openenergymonitor/emonpi2/docs/img/serial_config.png

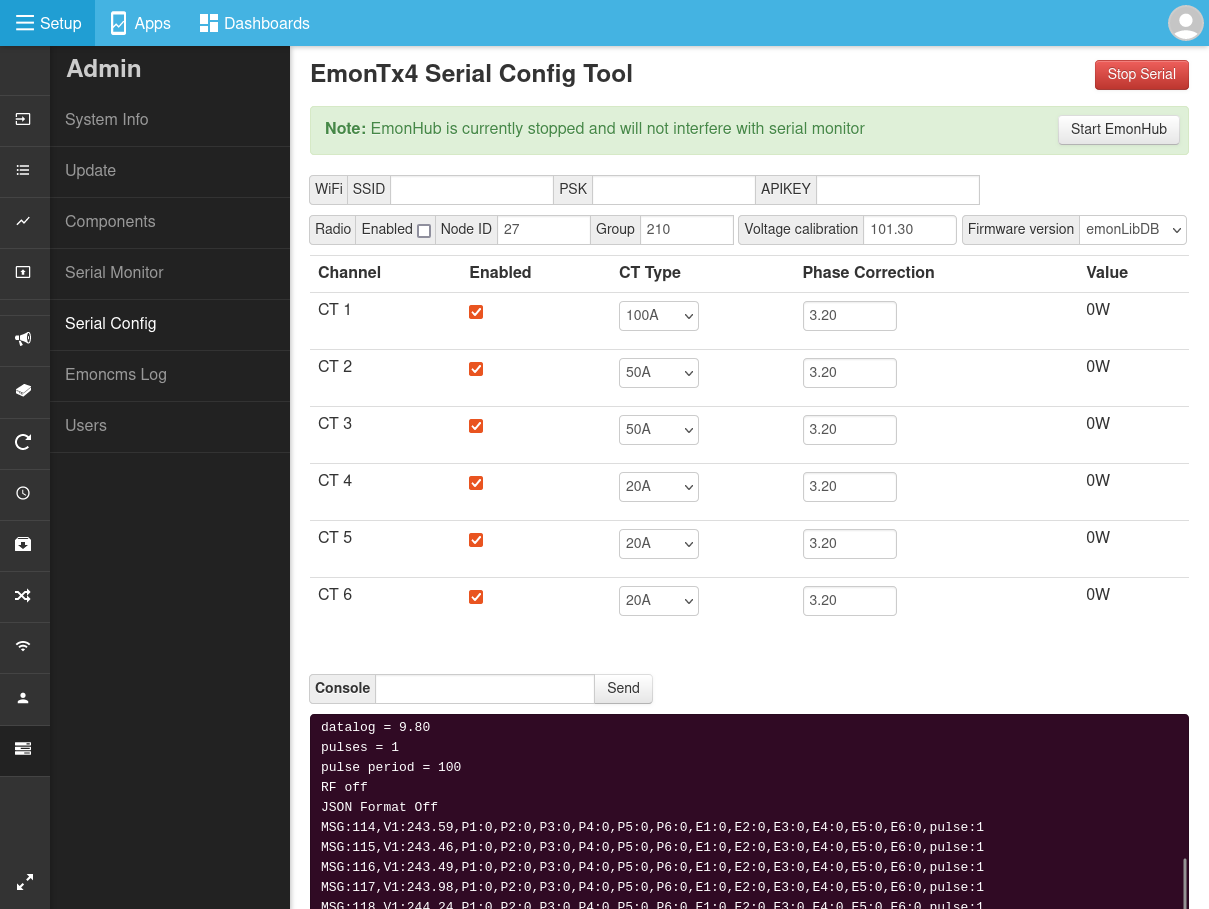
docs/img/serial_config.png
