openenergymonitor/emonpi2/firmware/img/compile_settings.png

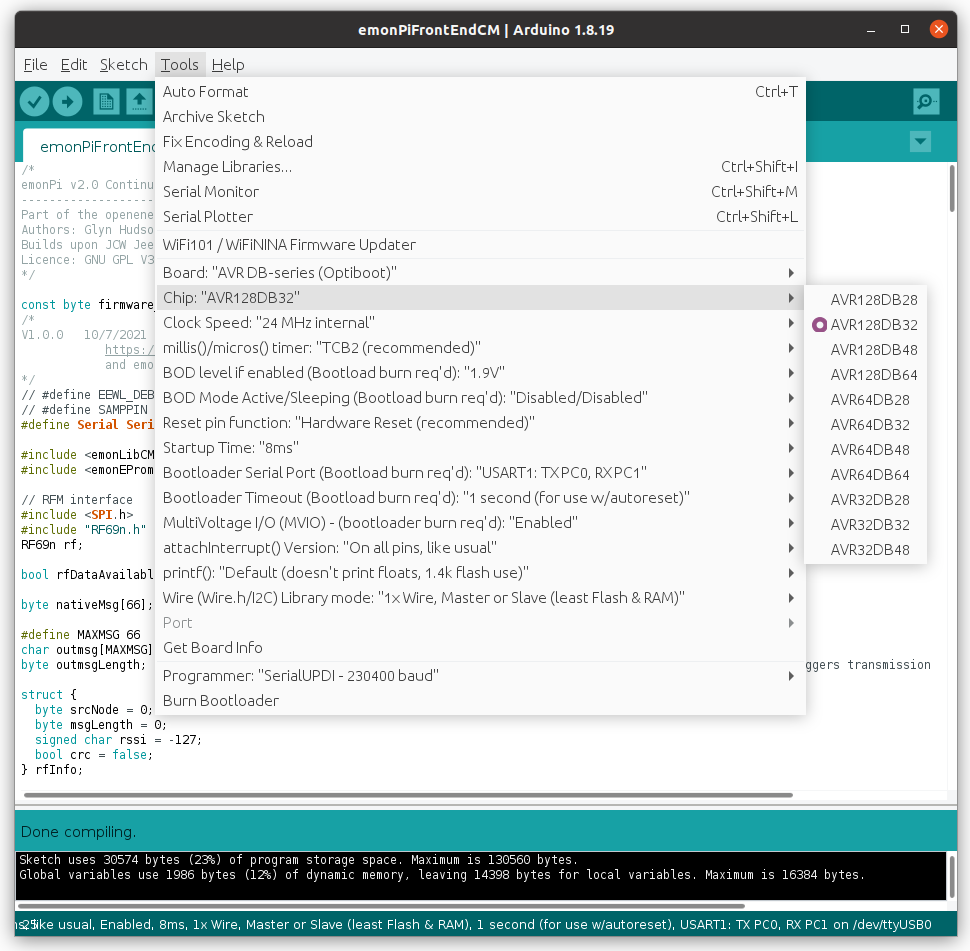
firmware/img/compile_settings.png
